maxhbr/zmk-stuff/mykeeb/rev4c/mykeeb-adapter/mykeeb-adapter.kicad_pcb

## KiCad design mykeeb/rev4c/mykeeb-adapter/mykeeb-adapter.kicad_pcb (2022-05-08)

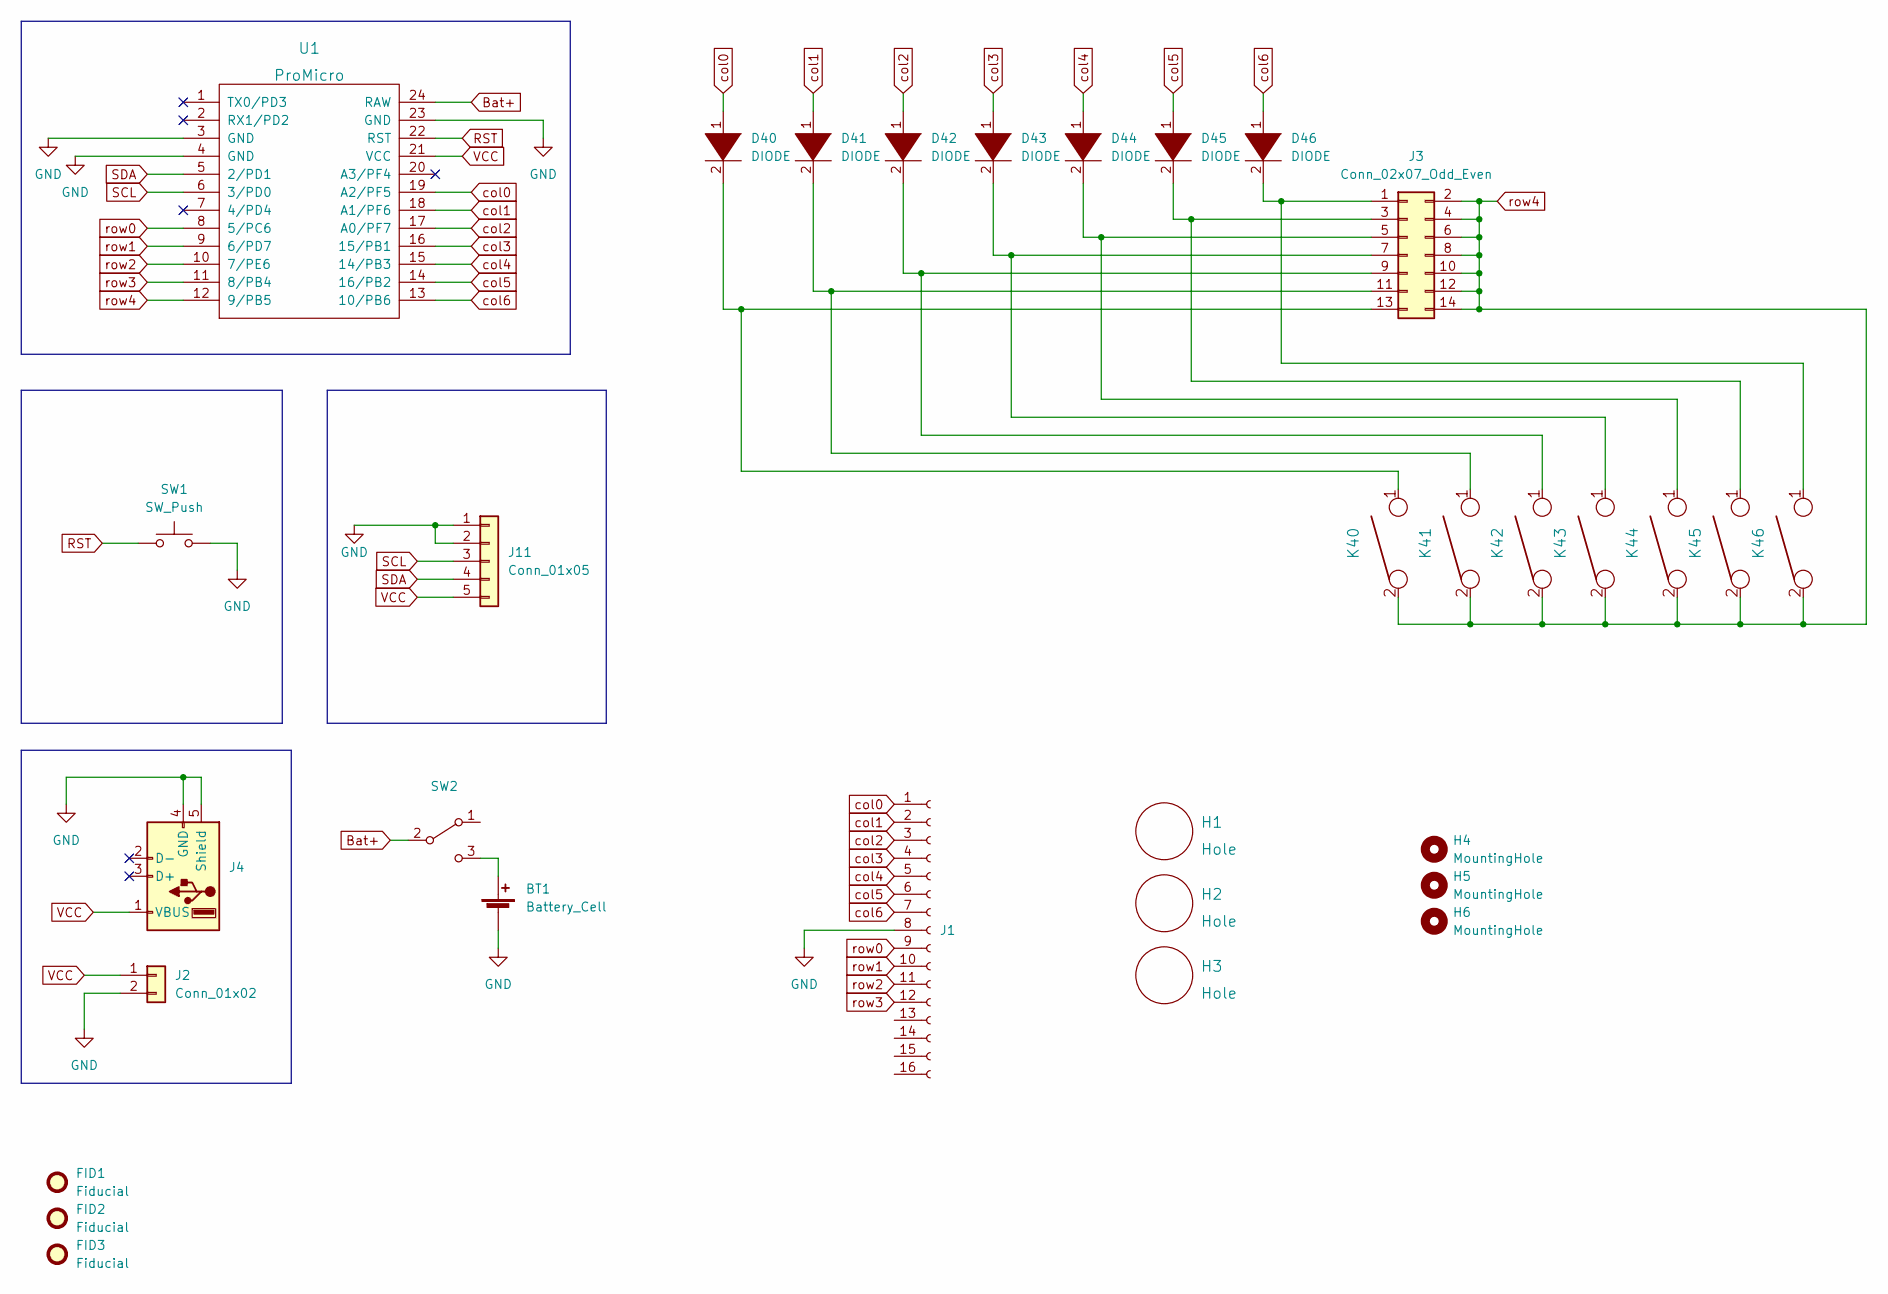
[picture p21: schematic mykeeb-adapter.kicad_sch, mykeeb]

Parts:
BT1: Battery_Cell; JST_PH_S2B-PH-K_1x02_P2.00mm_Horizontal
D40, D41, D42, D43, D44, D45, D46: DIODE; my_dual_D_SOD123F_v2b
FID1, FID2, FID3: Fiducial; Fiducial_1mm_Mask2mm
H1, H2, H3: Hole; breakaway
H4, H5, H6: MountingHole; MountingHole_3.2mm_M3
J1, J4: (no value)
J2: Conn_01x02; PinHeader_1x02_P2.54mm_Vertical
J3: Conn_02x07_Odd_Even; PinHeader_2x07_P2.54mm_Vertical
J11: Conn_01x05; PinSocket_1x05_P2.54mm_Vertical
K40, K41, K43, K44, K45, K46: KEYSW; Kailh_socket_MX_reversible_1u
K42: KEYSW; Kailh_socket_MX_reversible_1.25u
SW1: SW_Push; SW_PUSH_6mm
SW2: (no value)
U1: ProMicro; my_reversible_Pro_Micro

Connections:
Bat+: SW2.2 (B), U1.24 (RAW)
GND: BT1.2 (-), J1.8, J2.2, J4.4 (GND), J4.5 (Shield), J11.1, J11.2, SW1.2, U1.3 (GND), U1.4 (GND), U1.23 (GND)
unnamed: BT1.1 (+), SW2.3 (C)
unnamed: D40.2 (A), J3.13, K40.1
unnamed: D41.2 (A), J3.11, K41.1
unnamed: D42.2 (A), J3.9, K42.1
unnamed: D43.2 (A), J3.7, K43.1
unnamed: D44.2 (A), J3.5, K44.1
unnamed: D45.2 (A), J3.3, K45.1
unnamed: D46.2 (A), J3.1, K46.1
RST: SW1.1, U1.22 (RST)
SCL: J11.3, U1.6 (3/PD0)
SDA: J11.4, U1.5 (2/PD1)
VCC: J2.1, J4.1 (VBUS), J11.5, U1.21 (VCC)
col0: D40.1 (K), J1.1, U1.19 (A2/PF5)
col1: D41.1 (K), J1.2, U1.18 (A1/PF6)
col2: D42.1 (K), J1.3, U1.17 (A0/PF7)
col3: D43.1 (K), J1.4, U1.16 (15/PB1)
col4: D44.1 (K), J1.5, U1.15 (14/PB3)
col5: D45.1 (K), J1.6, U1.14 (16/PB2)
col6: D46.1 (K), J1.7, U1.13 (10/PB6)
row0: J1.9, U1.8 (5/PC6)
row1: J1.10, U1.9 (6/PD7)
row2: J1.11, U1.10 (7/PE6)
row3: J1.12, U1.11 (8/PB4)
row4: J3.2, J3.4, J3.6, J3.8, J3.10, J3.12, J3.14, K40.2, K41.2, K42.2, K43.2, K44.2, K45.2, K46.2, U1.12 (9/PB5)

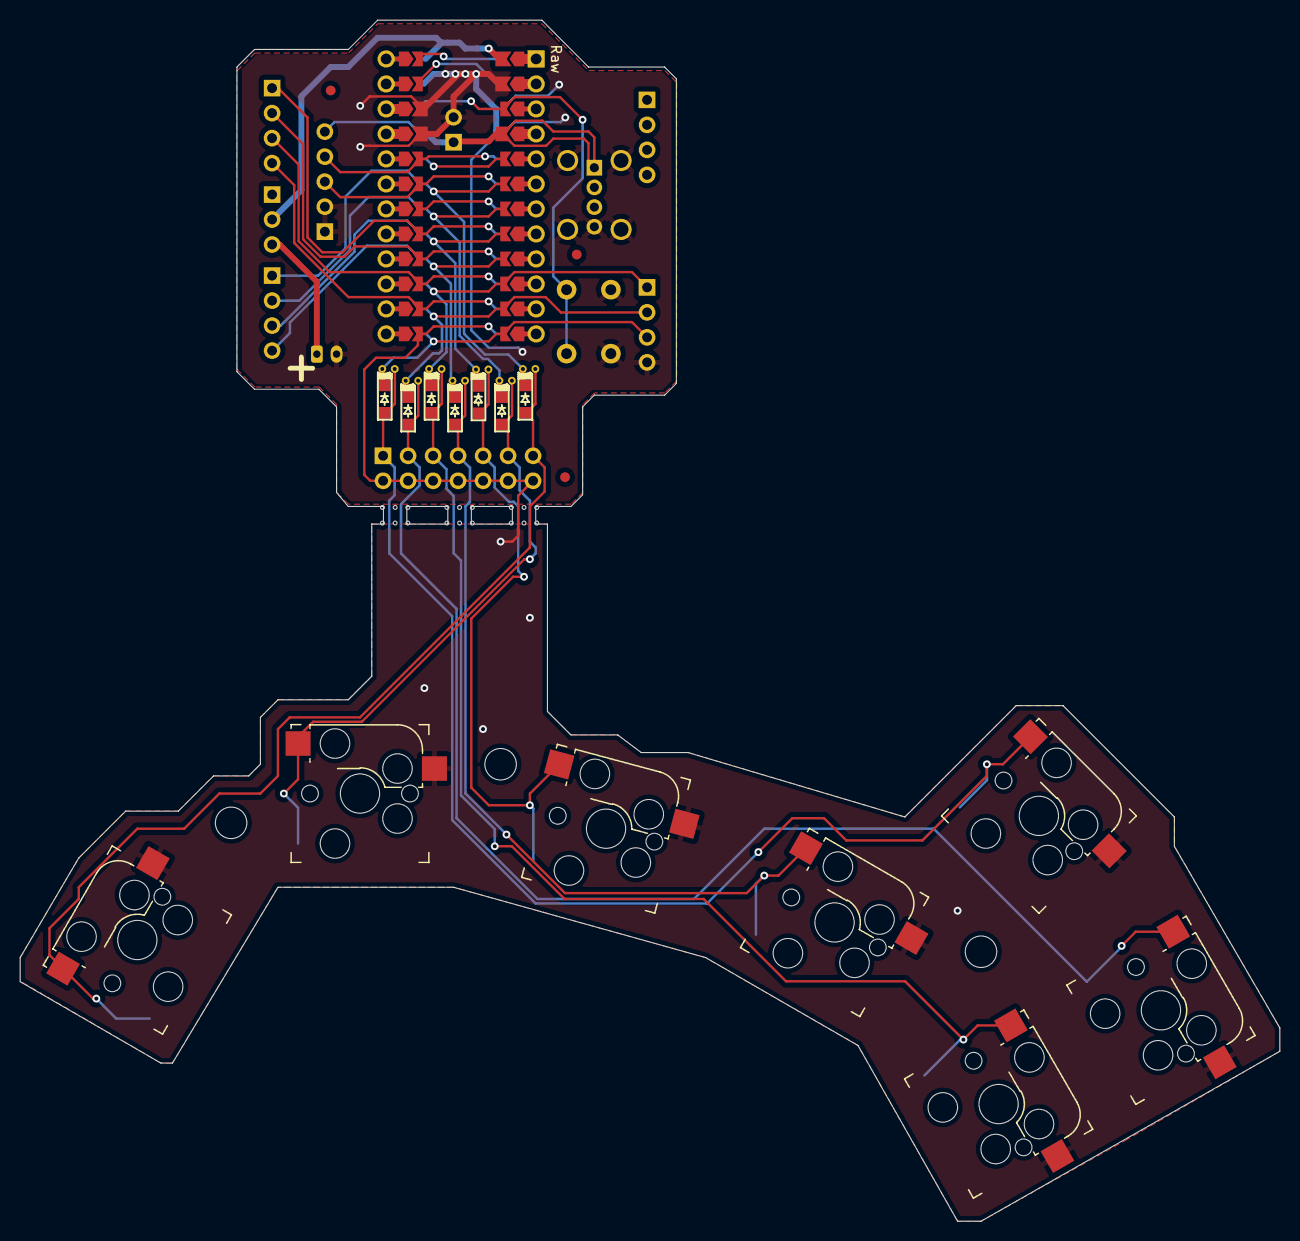
[picture p22: board mykeeb-adapter.kicad_pcb from above]

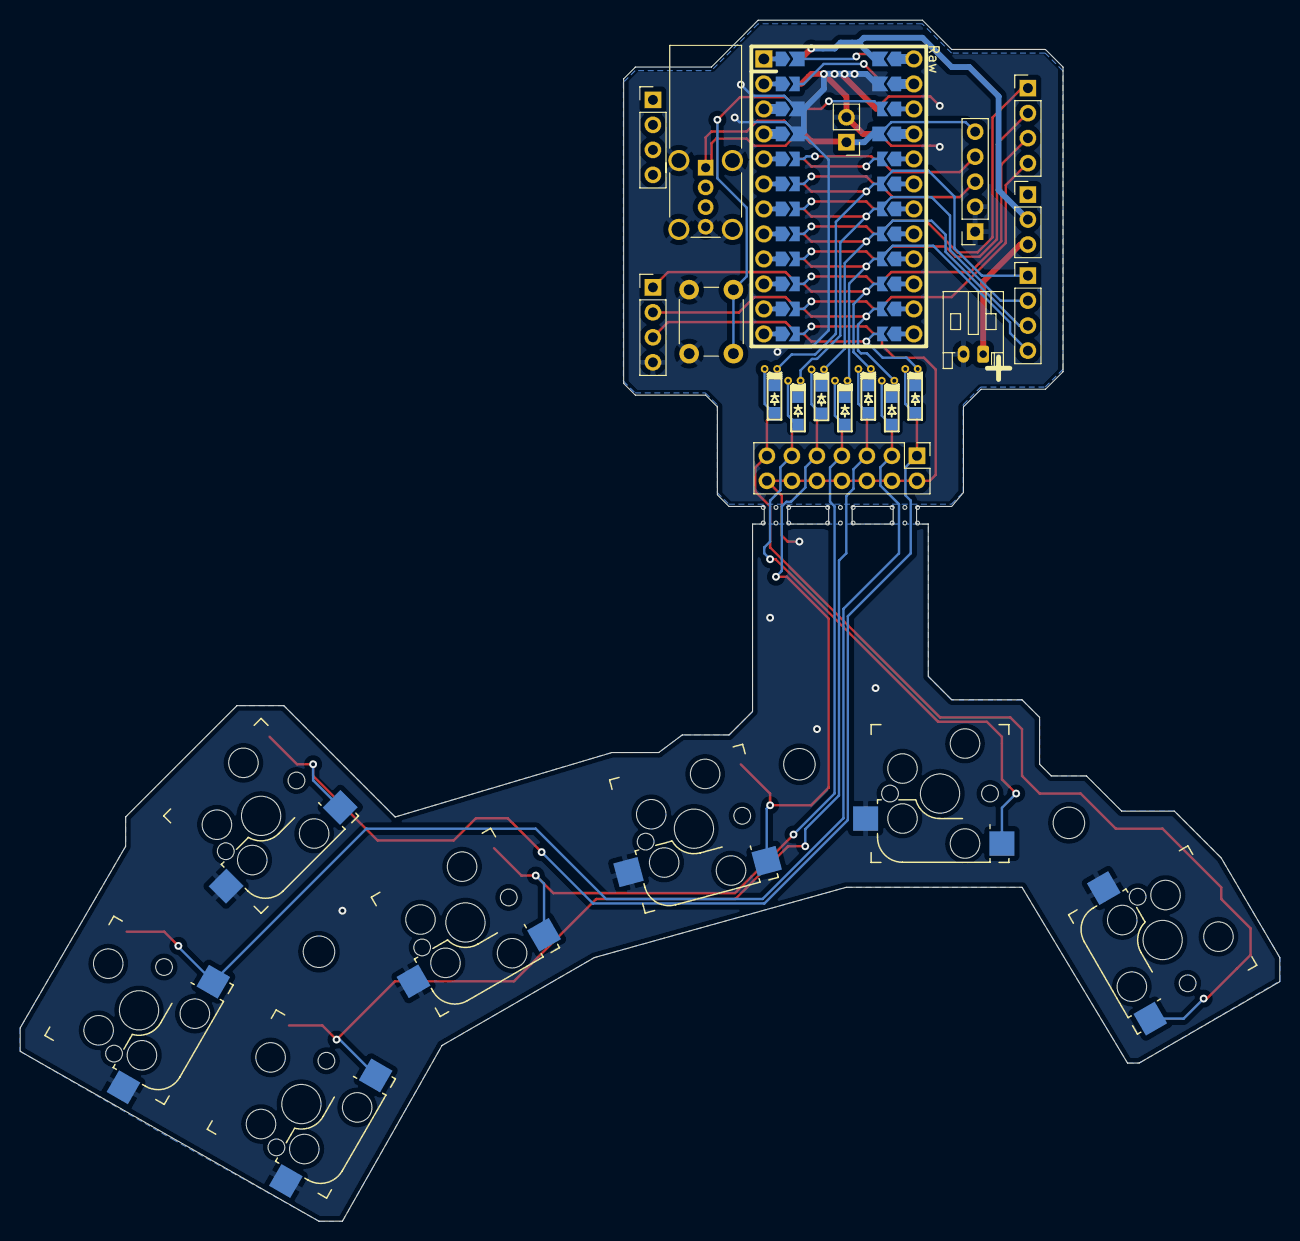
[picture p23: board mykeeb-adapter.kicad_pcb from below]

Board: 2 copper layers, 128.0 x 122.0 mm, 32 parts (8 on the bottom side), 26 nets.
